SolderedElectronics/GNSS-GPS-L86-M33-breakout-hardware-design/OUTPUTS/V1.2.0/333201.jpg

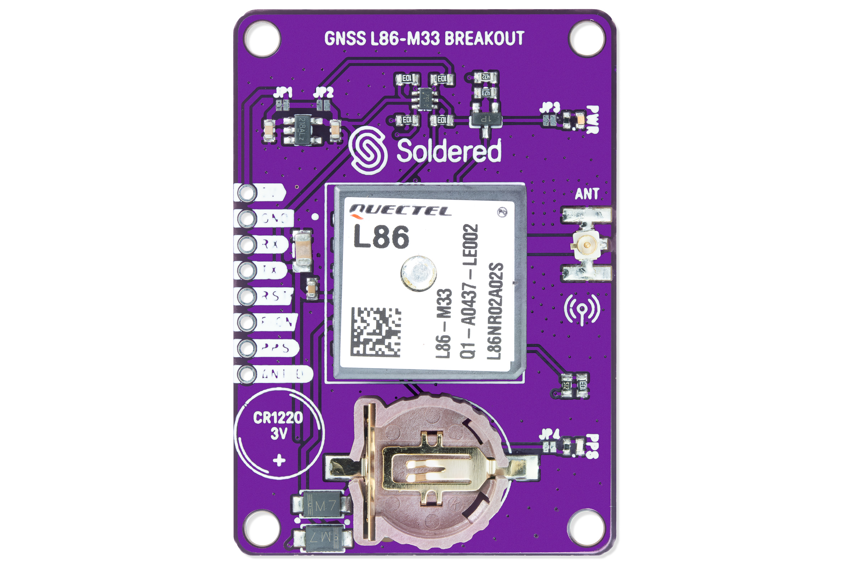
OUTPUTS/V1.2.0/333201.jpg
